amin-amani/SurenaHandMultiLayer/Documentation/bmp280_clock2.jpg

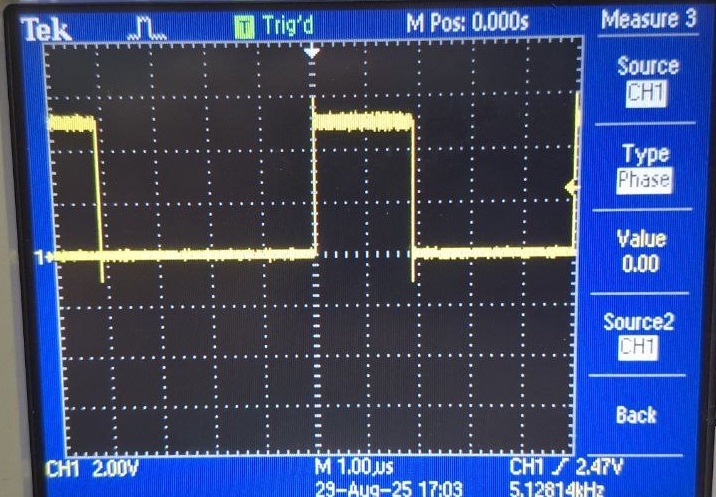
Documentation/bmp280_clock2.jpg
