amin-amani/SurenaHandMultiLayer/Documentation/error.jpg

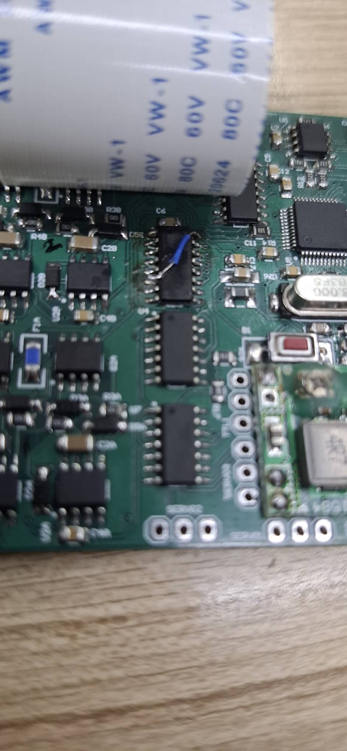
Documentation/error.jpg
