amin-amani/SurenaHandMultiLayer/Documentation/p1.PNG

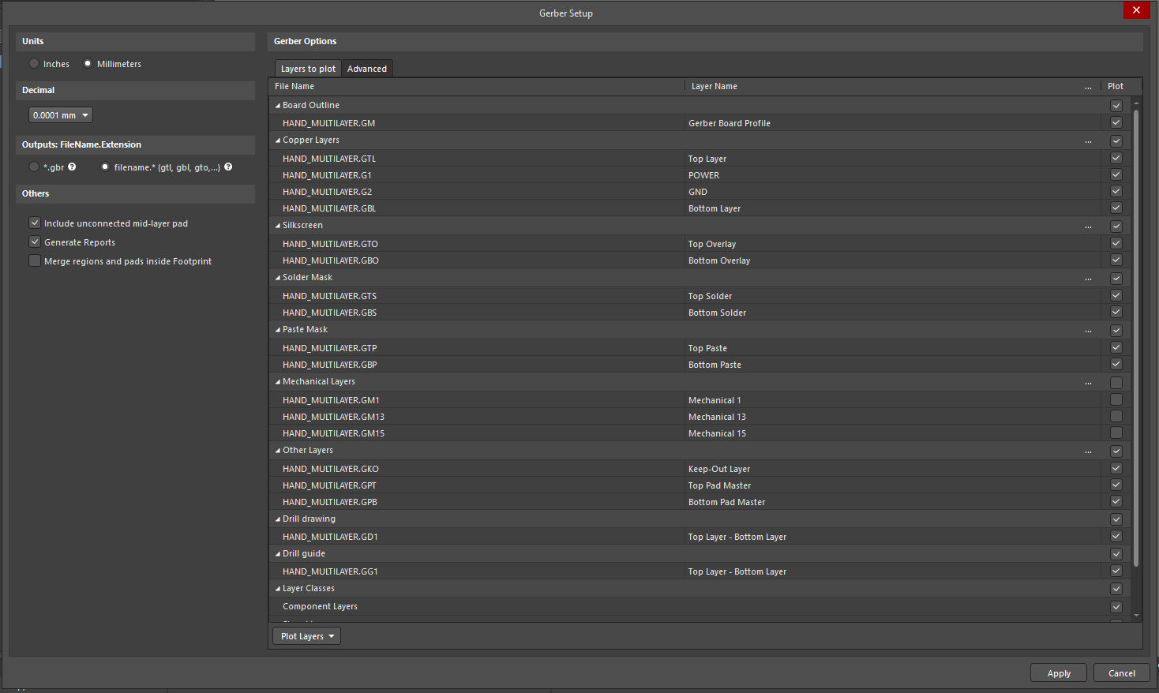
Documentation/p1.PNG
