amin-amani/SurenaHandMultiLayer/Documentation/p2.PNG

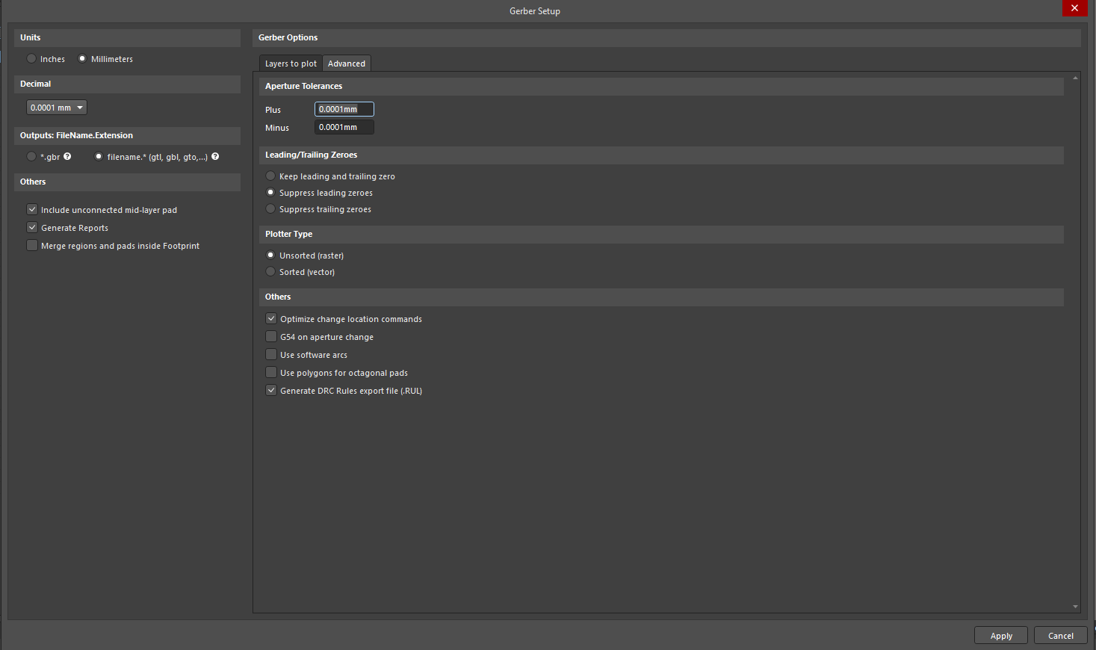
Documentation/p2.PNG
