amin-amani/SurenaHandMultiLayer/Documentation/p3.PNG

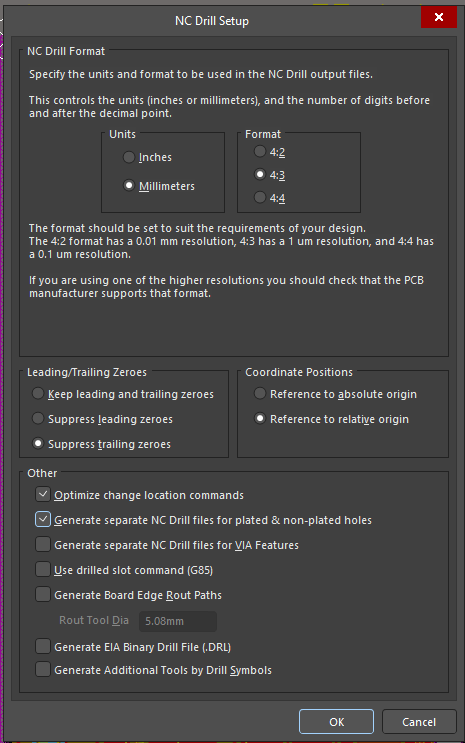
Documentation/p3.PNG
