amin-amani/SurenaHandMultiLayer/Documentation/sensor-connection.jpeg

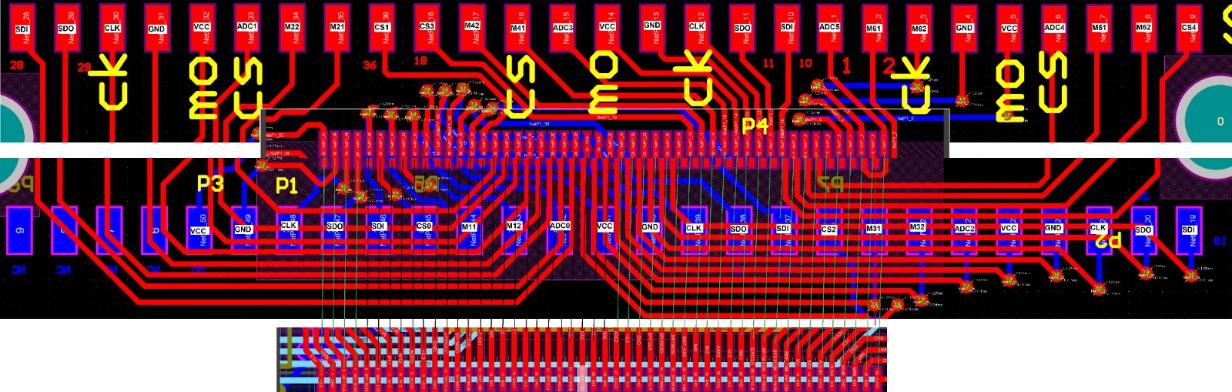
Documentation/sensor-connection.jpeg
