amin-amani/SurenaHandMultiLayer/firmware/test/logic_test_runner.c

#include <unity.h>
#include <unity_fixture.h>

TEST_GROUP_RUNNER(LOGIC_TEST_GROUP)
{

    RUN_TEST_CASE(LOGIC_TEST_GROUP, test_under_const);
//    RUN_TEST_CASE(LOGIC_TEST_GROUP, when_log_init_call_pid_elements_is_not_null);
//    RUN_TEST_CASE(LOGIC_TEST_GROUP, when_sensor_reached_max_position_trigger_should_change_to_zero);
//    RUN_TEST_CASE(LOGIC_TEST_GROUP, when_sensor_reached_max_pressure_trigger_should_change_to_zero);
//    RUN_TEST_CASE(LOGIC_TEST_GROUP, when_sensor_reached_middle_position_motor_speed_is_not_zero);
}
